MalphasWats/Mage/data/map.png

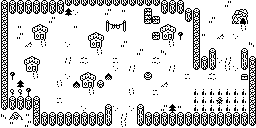
data/map.png
