MalphasWats/Mage/references/characters.png

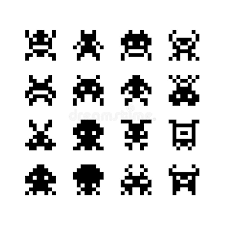
references/characters.png
