MalphasWats/Mage/glyphs.h

#ifndef GLYPHS_H
# define GLYPHS_H

#include <avr/pgmspace.h>

#define DIGIT_OFFSET 1
#define PLAYER_OFFSET 11

static const byte GLYPHS[] PROGMEM = {
    0x00, 0x00, 0x00, 0x00, 0x00, 0x00, 0x00, 0x00, // SPACE
    
    0x00, 0x3E, 0x7F, 0x4D, 0x59, 0x7F, 0x3E, 0x00, // 0
    0x00, 0x11, 0x31, 0x7F, 0x7F, 0x01, 0x01, 0x00, // 1
    0x00, 0x23, 0x67, 0x4D, 0x49, 0x79, 0x31, 0x00, // 2
    0x00, 0x22, 0x63, 0x49, 0x49, 0x7F, 0x36, 0x00, // 3
    0x00, 0x0C, 0x1C, 0x32, 0x7F, 0x7F, 0x04, 0x00, // 4
    0x00, 0x72, 0x73, 0x51, 0x51, 0x5F, 0x4E, 0x00, // 5
    0x00, 0x1E, 0x3F, 0x69, 0x49, 0x4F, 0x06, 0x00, // 6
    0x00, 0x40, 0x47, 0x4F, 0x58, 0x70, 0x60, 0x00, // 7
    0x00, 0x36, 0x7F, 0x49, 0x49, 0x7F, 0x36, 0x00, // 8
    0x00, 0x30, 0x79, 0x49, 0x4B, 0x7E, 0x3C, 0x00, // 9
    
    // MOBS
    0x00, 0x08, 0x13, 0x6c, 0x6c, 0x13, 0x08, 0x00, // Player (11)
    0x18, 0xd3, 0x76, 0x3c, 0x3c, 0x76, 0xd3, 0x18, 
    0x61, 0x9a, 0x2f, 0x34, 0x34, 0x2f, 0x9a, 0x61, 
    0x00, 0x00, 0x05, 0x16, 0x05, 0x00, 0x00, 0x00, 
    0x60, 0xbf, 0x2e, 0x34, 0x34, 0x2e, 0xbf, 0x60, 
    0x00, 0x00, 0x29, 0x5e, 0x2b, 0x00, 0x00, 0x00, 
    0x00, 0x10, 0x13, 0xdc, 0xdc, 0x13, 0x08, 0x00, 
    0x00, 0x01, 0x07, 0x0d, 0x0f, 0x0d, 0x07, 0x01, 
    0x31, 0x7b, 0xee, 0xff, 0xff, 0xee, 0x7b, 0x31, 
    0x42, 0xdb, 0x3c, 0x2e, 0x39, 0x2e, 0xdb, 0x42, 
    
    // Items
    0xc0, 0xa0, 0x50, 0x2a, 0x16, 0x0c, 0x1a, 0x01, // Sword (21)
    0x38, 0x76, 0x7f, 0x3f, 0x3f, 0x7f, 0x76, 0x38, // Armour
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
	0x00, 0x00, 0xf8, 0x04, 0x04, 0xc4, 0x24, 0x24, // window bl
	0x24, 0x24, 0xc4, 0x04, 0x04, 0xf8, 0x00, 0x00, // window br
	0x24, 0x24, 0x24, 0x24, 0x24, 0x24, 0x24, 0x24, // window tb
    0x00, 0x00, 0xff, 0x00, 0x00, 0xff, 0x00, 0x00, // window lr
};


/* Interface */



#endif
